daveho/HexClock/hw_proto/HexClock.sch

## KiCad design hw_proto/HexClock.sch (2019-05-11)

Schematic: HexClock.sch

Parts:
AFF1, AFF2, AFF3, AFF4: LTS-6960HR; 7SegmentLED_LTS6760_LTS6780
J1: Screw_Terminal_01x02
Q1, Q2, Q3, Q4: 2N3906
R1, R2, R3, R4, R5, R6, R7, R8: R
R9, R12, R13, R14: 4k7
R10, R11: 1k
SW1, SW2, SW3: SW_Push
TB1: ARDUINO_NANO; SHIELD_ARDUINO_NANO
U1: DS1307+; DIP-8_W7.62mm
Y1: 32.768 KHz

Notes on the sheet:
Hex clock using Arduino Nano and DS1307 RTC
Power connector
